David-OC17/MedWay/analysis/images/humidity_example.png

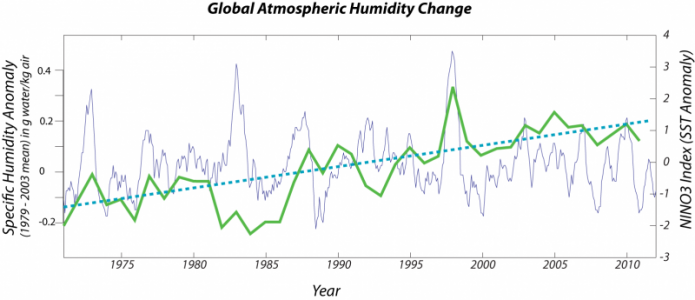
analysis/images/humidity_example.png
