David-OC17/MedWay/analysis/images/temperature_example.png

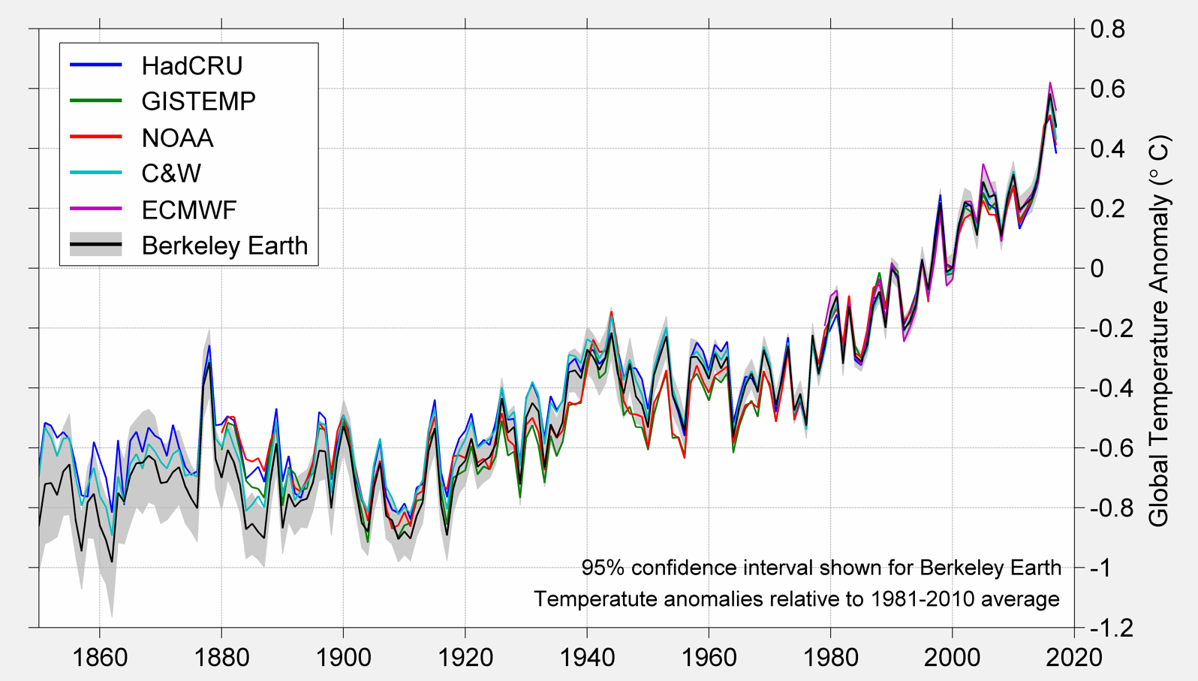
analysis/images/temperature_example.png
