David-OC17/MedWay/images/analytics.png

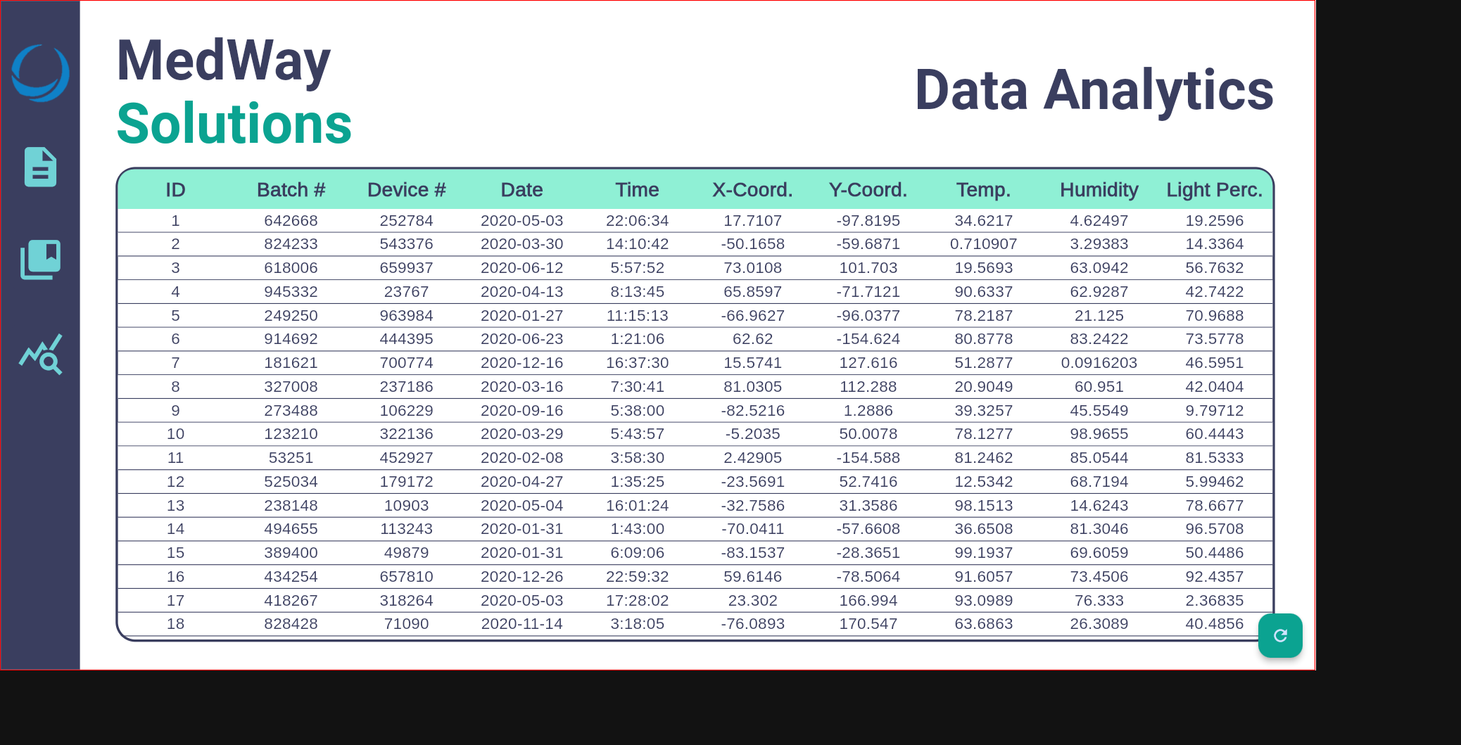
images/analytics.png
